onurkarakoc79/Cargo-Damage-Detection-System/Codes/src/MPULib1/MPU6050REG.hpp

#ifndef MPU6050REG_HPP
#define MPU6050REG_HPP


#define MPU6050_ADDRESS 0x68
#define MPU6050_GYROREG 0x43
#define MPU6050_ACCELREG 0x3B
#define MPU6050_ACCEL_RANGEREG 0x1C
#define MPU6050_FILTERREG 0x1A
#define MPU6050_SENSITIVITYREG 0x1B
#define MPU6050_SLEEPREG 0x6B

#define MPU6050_INT_PIN_CFG 0x37
#define MPU6050_MOTION_THR 0x1F
#define MPU6050_MOTION_DUR 0x20
#define MPU6050_INT_ENABlE 0x38


#define GYRO_MESSAGE_BYTES 6
#define ACCEL_MESSAGE_BYTES 6


#endif // MPU6050REG_HPP
